vergoh/micropython-spotify-status-display/src/spotify_api.py

# MIT License
# Copyright (c) 2020 Teemu Toivola
# https://github.com/vergoh/micropython-spotify-status-display

import gc
import time
from micropython import const

# imports from additional files
import uurequests as requests
from helpers import b64encode, urlencode

_spotify_account_api_base = const("https://accounts.spotify.com/api")
_spotify_api_base = const("https://api.spotify.com")

def _spotify_api_request(method, url, data = None, headers = None, retry = True):
    ret = {'status_code': 0, 'json': {}, 'text': 'No reply content'}
    print("{} {}".format(method, url))
    try:
        r = requests.request(method, url, data = data, headers = headers, parse_headers = False)
    except OSError as e:
        print("OSError: {}".format(e))
        ret['text'] = str(e)
        r = None

    if r is None or r.status_code < 200 or r.status_code >= 500:
        if retry:
            if r is None:
                print("failed, retrying...")
            elif r is not None:
                print("status {}, retrying...".format(r.status_code))
                r.close()
                del r
            time.sleep_ms(500)
            return _spotify_api_request(method, url, data = data, headers = headers, retry = False)
        else:
            return ret

    ret['status_code'] = r.status_code
    try:
        ret['json'] = r.json()
    except Exception as e:
        if r.status_code == 200 and method == "GET":
            print("json decoding failed: {}".format(e))
            if retry:
                if r is not None:
                    r.close()
                    del r
                print("retrying...")
                time.sleep_ms(500)
                gc.collect()
                return _spotify_api_request(method, url, data = data, headers = headers, retry = False)
            ret['status_code'] = 0
            ret['json'] = {'exception': 1}
            # Avoid allocating response body here; memory is likely already tight.
            ret['text'] = str(e)

    if len(ret['json']) == 0:
        # Only keep a small body prefix for debugging (avoid full buffering/decoding).
        try:
            if r.status_code < 200 or r.status_code >= 300:
                body_prefix = r.read(256)
                if body_prefix:
                    try:
                        ret['text'] = body_prefix.decode("utf-8")
                    except Exception:
                        ret['text'] = str(body_prefix)
        except Exception:
            pass

    try:
        r.close()
    except:
        pass

    del r
    return ret

def get_api_tokens(authorization_code, redirect_uri, client_id, client_secret):
    spotify_token_api_url = "{}/token".format(_spotify_account_api_base)
    reqdata = { 'grant_type': 'authorization_code', 'code': authorization_code, 'redirect_uri': redirect_uri }

    b64_auth = "Basic {}".format(b64encode(b"{}:{}".format(client_id, client_secret)).decode())
    headers = { 'Content-Type': 'application/x-www-form-urlencoded', 'Authorization': b64_auth }

    return _spotify_api_request("POST", spotify_token_api_url, data = urlencode(reqdata), headers = headers)

def refresh_access_token(api_tokens, client_id, client_secret):
    spotify_token_api_url = "{}/token".format(_spotify_account_api_base)
    reqdata = { 'grant_type': 'refresh_token', 'refresh_token': api_tokens['refresh_token'] }

    b64_auth = "Basic {}".format(b64encode(b"{}:{}".format(client_id, client_secret)).decode())
    headers = { 'Content-Type': 'application/x-www-form-urlencoded', 'Authorization': b64_auth }

    return _spotify_api_request("POST", spotify_token_api_url, data = urlencode(reqdata), headers = headers)

def get_currently_playing(api_tokens):
    spotify_player_api_url = "{}/v1/me/player/currently-playing?additional_types=track,episode".format(_spotify_api_base)
    headers = { 'Authorization': "Bearer {}".format(api_tokens['access_token']) }

    return _spotify_api_request("GET", spotify_player_api_url, headers = headers)

def get_current_device_id(api_tokens):
    spotify_player_api_url = "{}/v1/me/player".format(_spotify_api_base)
    headers = { 'Authorization': "Bearer {}".format(api_tokens['access_token']) }

    return _spotify_api_request("GET", spotify_player_api_url, headers = headers)

def pause_playback(api_tokens):
    spotify_player_api_url = "{}/v1/me/player/pause".format(_spotify_api_base)
    headers = { 'Authorization': "Bearer {}".format(api_tokens['access_token']) }

    return _spotify_api_request("PUT", spotify_player_api_url, headers = headers)

def resume_playback(api_tokens, device_id = None):
    spotify_player_api_url = "{}/v1/me/player/play".format(_spotify_api_base)
    headers = { 'Authorization': "Bearer {}".format(api_tokens['access_token']) }
    if device_id is not None:
        spotify_player_api_url += "?device_id={}".format(device_id)

    return _spotify_api_request("PUT", spotify_player_api_url, headers = headers)

def next_playback(api_tokens, device_id = None):
    spotify_player_api_url = "{}/v1/me/player/next".format(_spotify_api_base)
    headers = { 'Authorization': "Bearer {}".format(api_tokens['access_token']) }
    if device_id is not None:
        spotify_player_api_url += "?device_id={}".format(device_id)

    return _spotify_api_request("POST", spotify_player_api_url, headers = headers)

def save_track(api_tokens, track_id):
    spotify_library_api_url = "{}/v1/me/library".format(_spotify_api_base)
    query = urlencode({'uris': 'spotify:track:{}'.format(track_id)})
    spotify_library_api_url += "?{}".format(query)
    headers = { 'Authorization': "Bearer {}".format(api_tokens['access_token']) }

    return _spotify_api_request("PUT", spotify_library_api_url, headers = headers)
