vergoh/micropython-spotify-status-display/src/helpers.py

# reduced from https://github.com/blainegarrett/urequests2

import binascii

always_safe = ('ABCDEFGHIJKLMNOPQRSTUVWXYZ'
               'abcdefghijklmnopqrstuvwxyz'
               '0123456789' '_.-')

def quote(s):
    res = []
    for c in s:
        if c in always_safe:
            res.append(c)
            continue
        res.append('%%%x' % ord(c))
    return ''.join(res)

def quote_plus(s):
    if ' ' in s:
        s = s.replace(' ', '+')
    return quote(s)

def urlencode(query):
    if isinstance(query, dict):
        query = query.items()
    l = []
    for k, v in query:
        if not isinstance(v, list):
            v = [v]
        for value in v:
            k = quote_plus(str(k))
            v = quote_plus(str(value))
            l.append(k + '=' + v)
    return '&'.join(l)

def b64encode(s):
    """Reproduced from micropython base64"""
    if not isinstance(s, (bytes, bytearray)):
        raise TypeError("expected bytes, not %s" % s.__class__.__name__)
    # Strip off the trailing newline
    encoded = binascii.b2a_base64(s)[:-1]
    return encoded
